dmachtey/ndom-bbb/images/20170901_104352.jpg

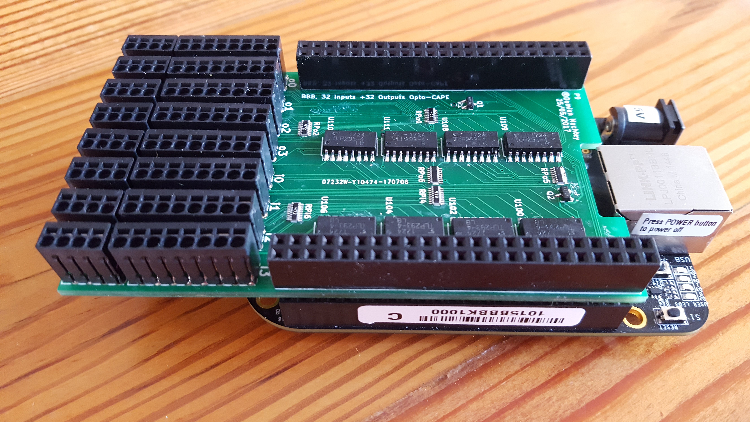
images/20170901_104352.jpg
