dmachtey/ndom-bbb/images/20170909_112535.jpg

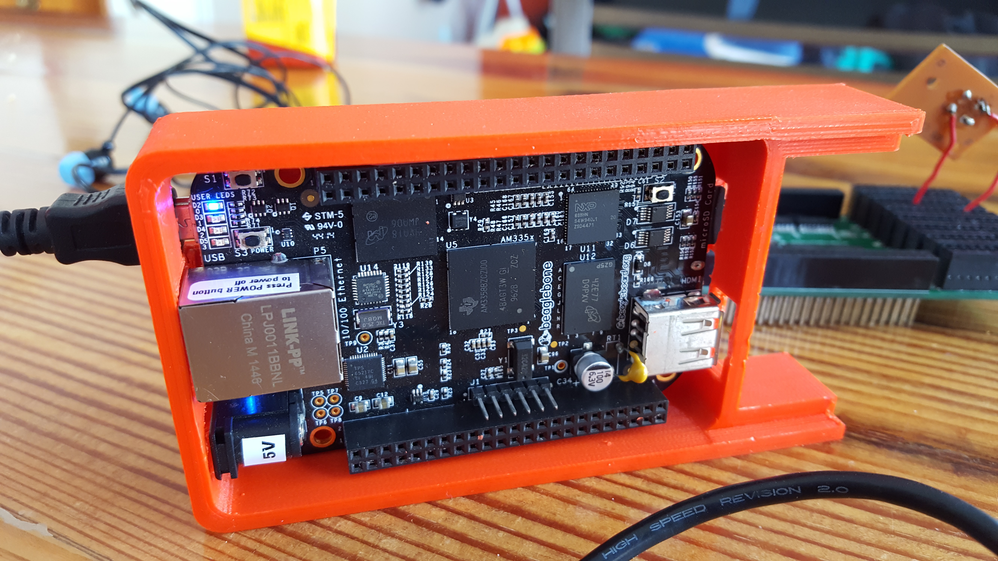
images/20170909_112535.jpg
