dmachtey/ndom-bbb/images/20170901_104410.jpg

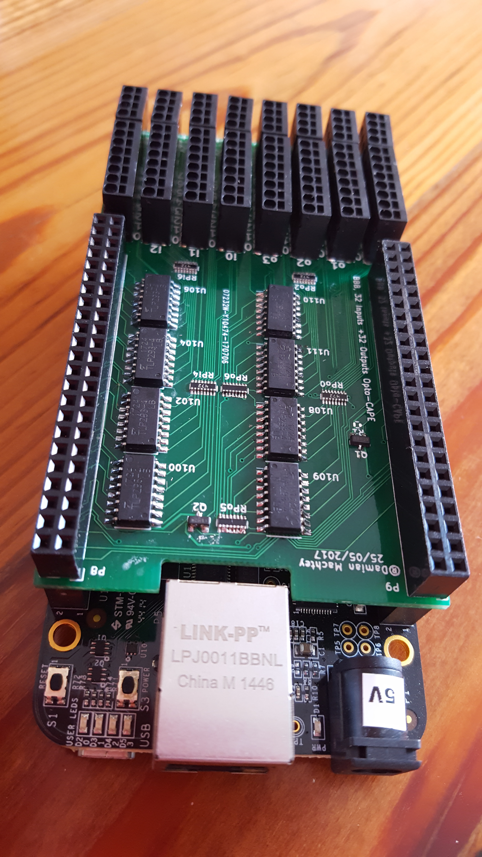
images/20170901_104410.jpg
