dmachtey/ndom-bbb/images/20170901_104416.jpg

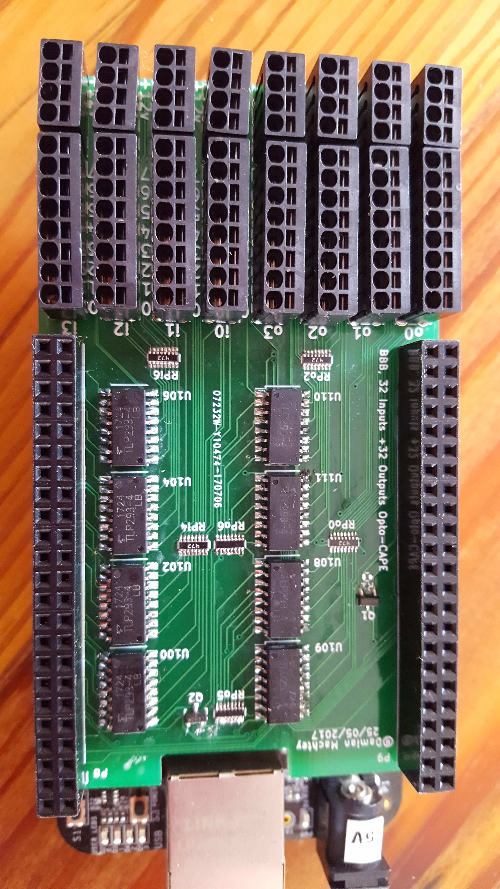
images/20170901_104416.jpg
