dmachtey/ndom-bbb/images/20170907_075249.jpg

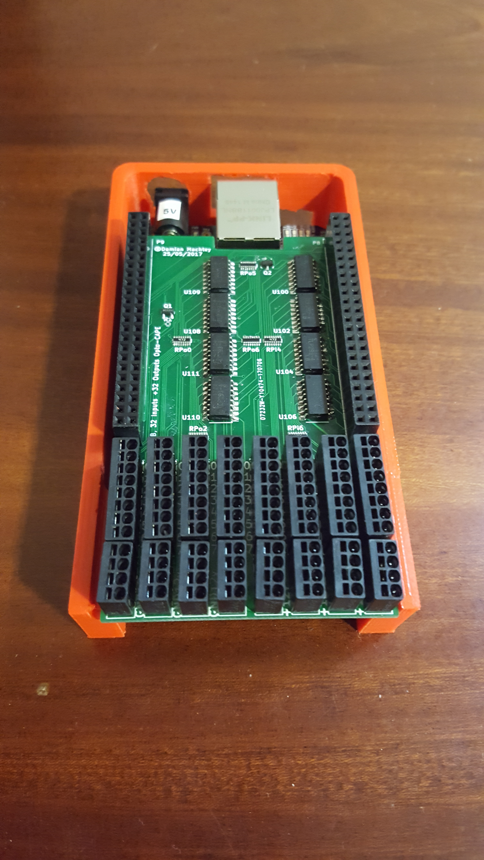
images/20170907_075249.jpg
